HarinarayananP/Air-polution-monitoring/POLMO Sofware/Node-Red Flows/Flows.png

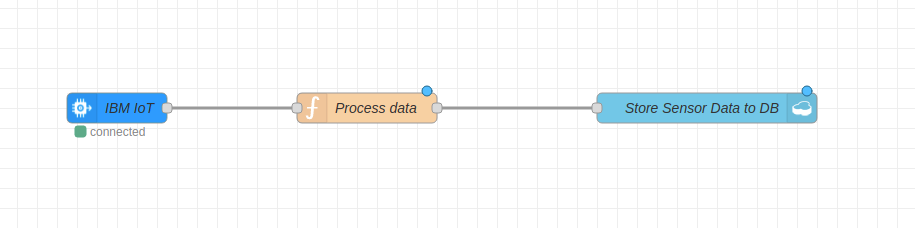
POLMO Sofware/Node-Red Flows/Flows.png
